ssbb/pipra/pcb/pipra.kicad_sch

## KiCad design pcb/pipra.kicad_sch (2025-05-22, an earlier design)

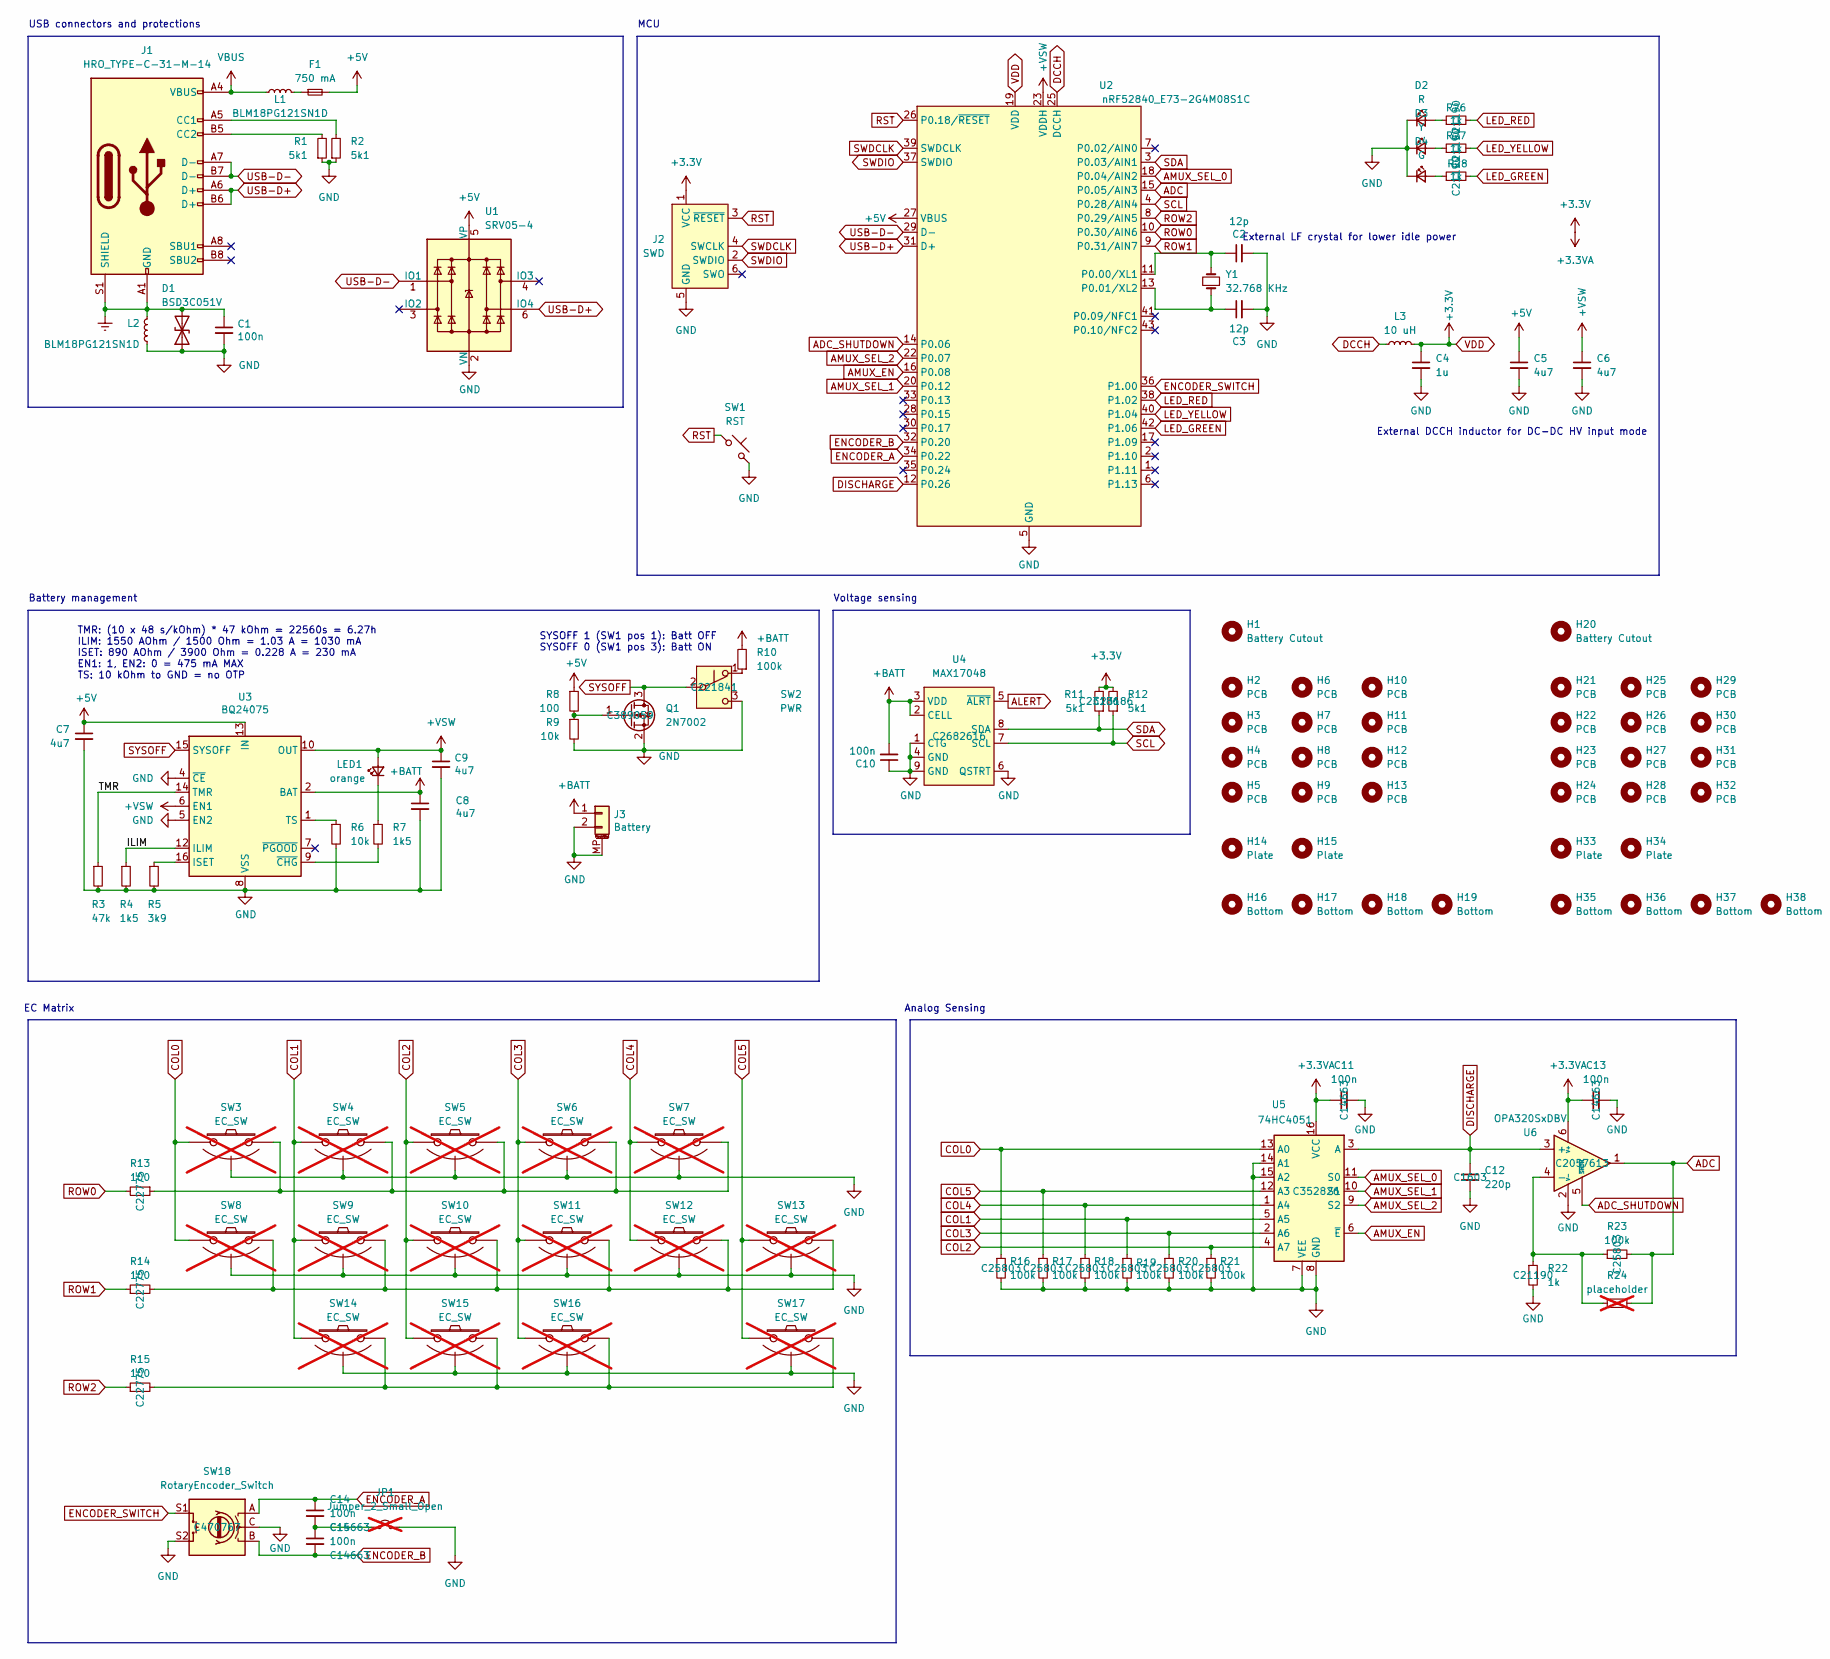
[picture p2: schematic pipra.kicad_sch, part in row 1, column 1]

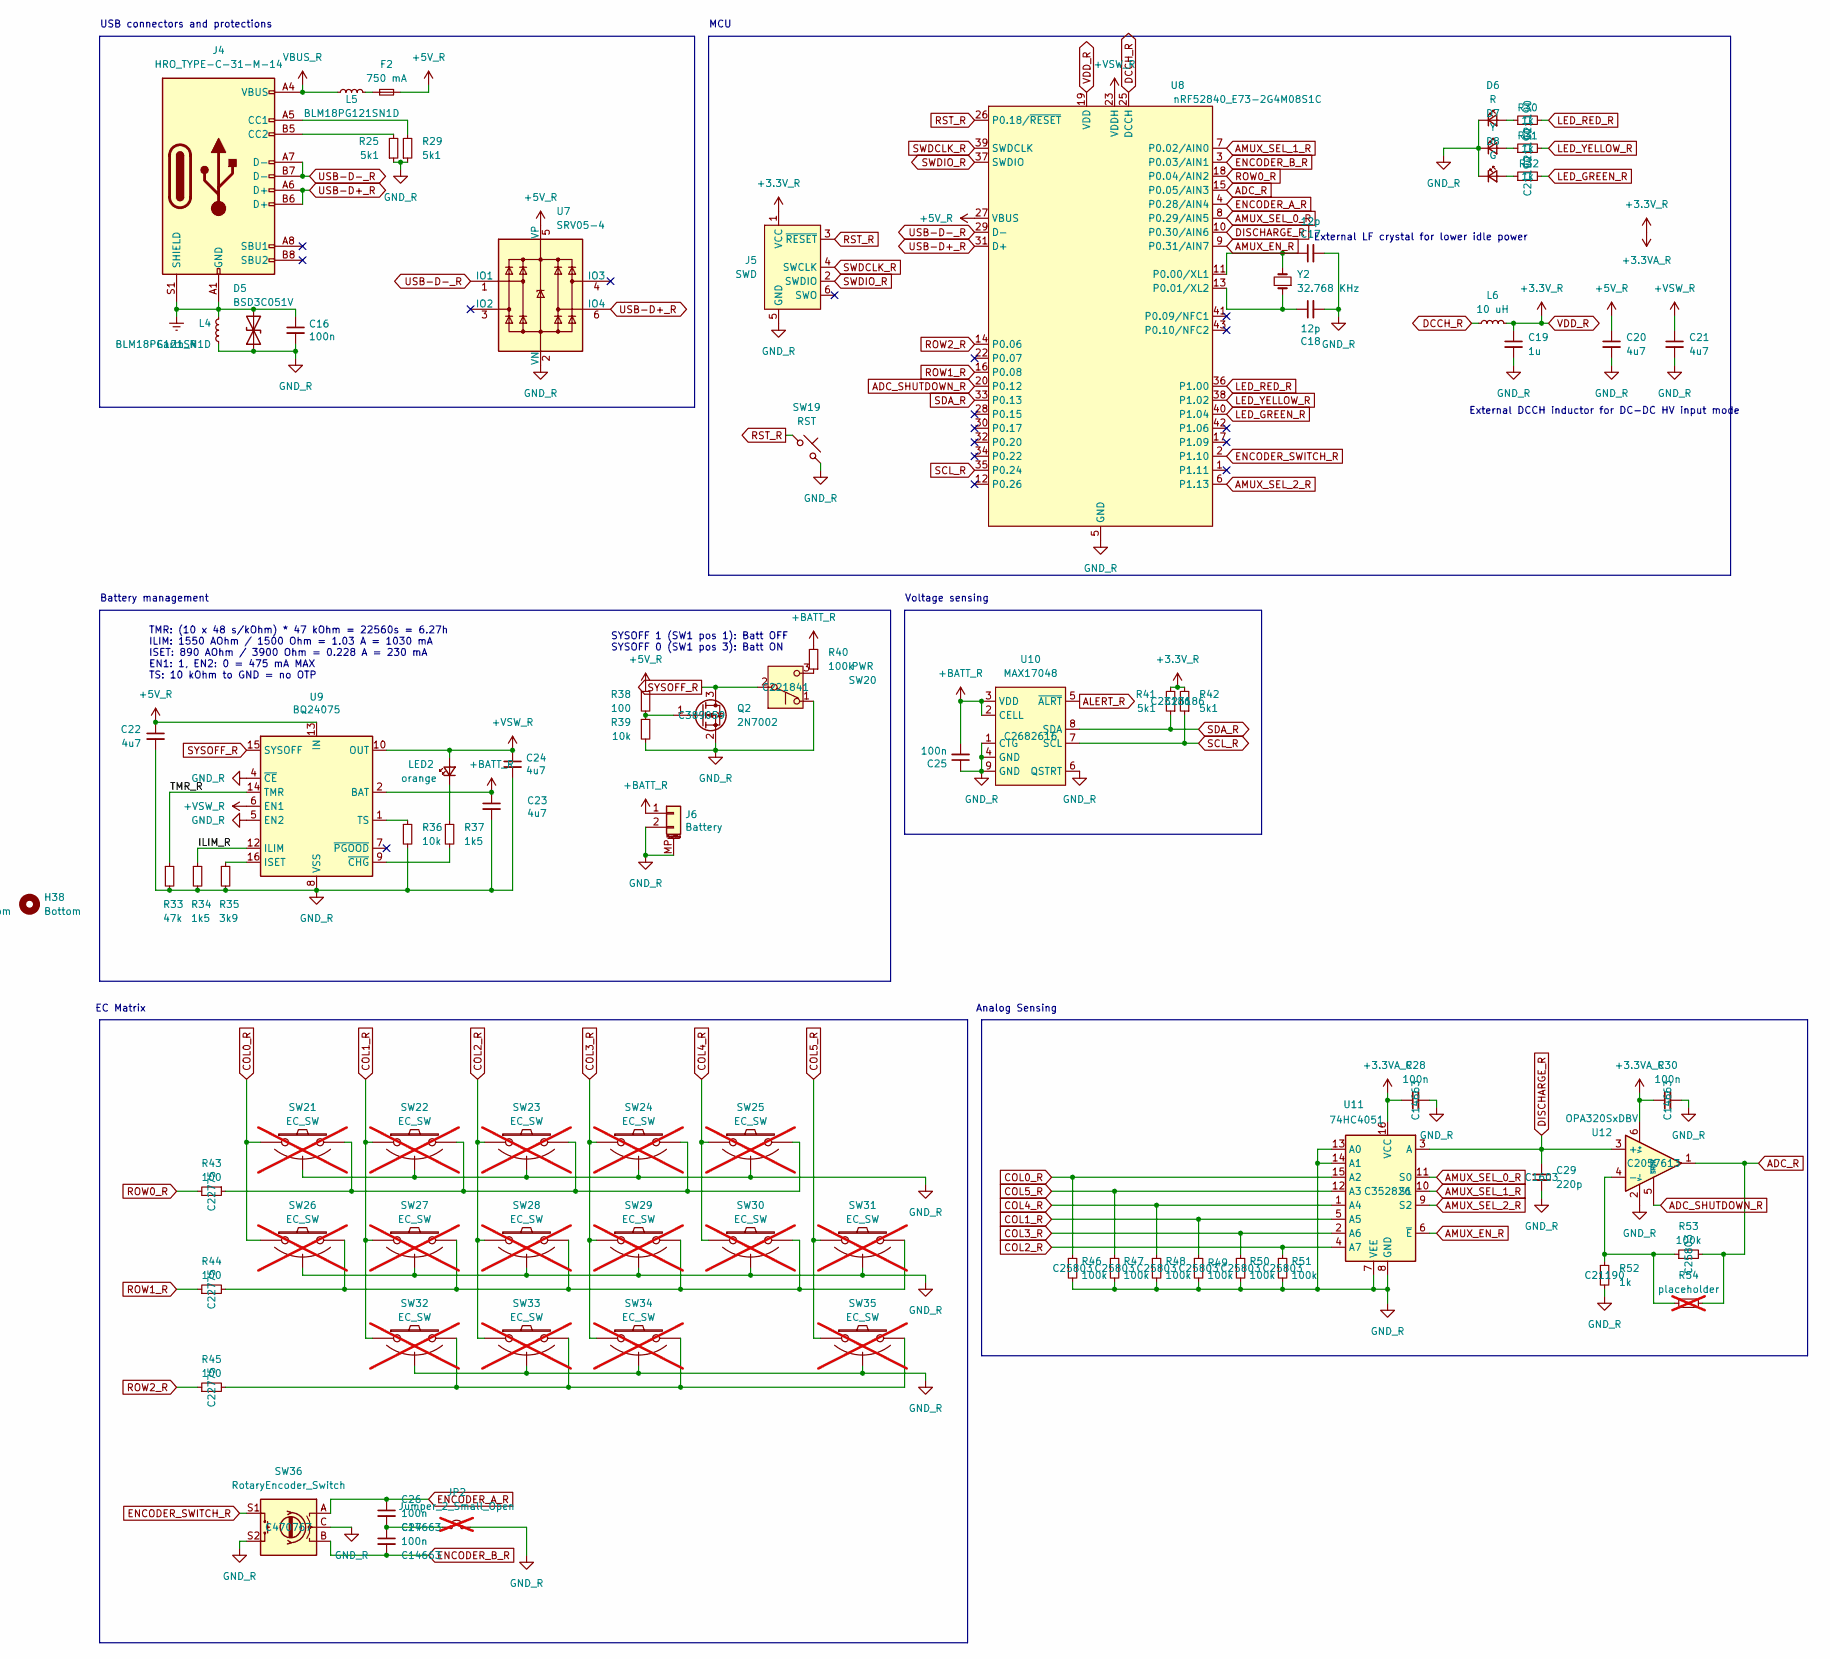
[picture p3: schematic pipra.kicad_sch, part in row 1, column 2]

Parts:
C1, C10, C11, C13, C14, C15, C16, C25, C26, C27, C28, C30: 100n; C_0603_1608Metric; LCSC C14663
C2, C3, C17, C18: 12p; C_0603_1608Metric; LCSC C38523
C4, C19: 1u; C_0603_1608Metric; LCSC C15849
C5, C6, C7, C8, C9, C20, C21, C22, C23, C24: 4u7; C_0603_1608Metric; LCSC C19666
C12, C29: 220p; C_0603_1608Metric; LCSC C1603
D1, D5: BSD3C051V; D_SOD-323; LCSC C151996
D2, D6: R; LED_D3.0mm; LCSC C2895165
D3, D7: Y; LED_D3.0mm; LCSC C2895167
D4, D8: G; LED_D3.0mm; LCSC C2895166
F1, F2: 750 mA; Fuse_0603_1608Metric; LCSC C914092
H1, H20: Battery Cutout; Battery_HAC-006
H2, H3, H4, H5, H6, H7, H8, H9, H10, H11, H12, H13, H21, H22, H23, H24, H25, H26, H27, H28, H29, H30, H31, H32: PCB; MountingHole_2.2mm_M2
H14, H15, H33, H34: Plate; MountingHole_4mm
H16, H17, H18, H19, H35, H36, H37, H38: Bottom; MountingHole_3.5mm
J1, J4: HRO_TYPE-C-31-M-14; USB_C_Receptacle_HRO_TYPE-C-31-M-12; LCSC C165948
J2, J5: SWD; CON_TC2030_outlined
J3, J6: Battery; Molex_Pico-EZmate_78171-0002_1x02-1MP_P1.20mm_Vertical; LCSC C505023
JP1, JP2: Jumper_2_Small_Open; SolderJumper-2_P1.3mm_Open_RoundedPad1.0x1.5mm; not fitted
L1, L2, L4, L5: BLM18PG121SN1D; L_0603_1608Metric; LCSC C14709
L3, L6: 10 uH; L_0603_1608Metric; LCSC C92982
LED1, LED2: orange; LED_0603_1608Metric; LCSC C401116
Q1, Q2: 2N7002; SOT-23; LCSC C389059
R1, R2, R11, R12, R25, R29, R41, R42: 5k1; R_0603_1608Metric; LCSC C23186
R3, R33: 47k; R_0603_1608Metric; LCSC C25819
R4, R7, R34, R37: 1k5; R_0603_1608Metric; LCSC C22843
R5, R35: 3k9; R_0603_1608Metric; LCSC C23018
R6, R9, R36, R39: 10k; R_0603_1608Metric; LCSC C25804
R8, R13, R14, R15, R38, R43, R44, R45: 100; R_0603_1608Metric; LCSC C22775
R10, R16, R17, R18, R19, R20, R21, R23, R40, R46, R47, R48, R49, R50, R51, R53: 100k; R_0603_1608Metric; LCSC C25803
R22, R26, R27, R28, R30, R31, R32, R52: 1k; R_0603_1608Metric; LCSC C21190
R24, R54: placeholder; R_0603_1608Metric; not fitted
SW1, SW19: RST; Panasonic_EVQPUL_EVQPUC; LCSC C79174
SW2, SW20: PWR; SW_SPDT_PCM12; LCSC C221841
SW3, SW4, SW5, SW6, SW7, SW8, SW9, SW10, SW11, SW12, SW13, SW14, SW15, SW16, SW17, SW21, SW22, SW23, SW24, SW25, SW26, SW27, SW28, SW29, SW30, SW31, SW32, SW33, SW34, SW35: EC_SW; EC_Pad_L84; not fitted
SW18, SW36: RotaryEncoder_Switch; RotaryEncoder_Alps_EC12E-Switch_Vertical_H20mm; LCSC C470767
U1, U7: SRV05-4; SOT-23-6; LCSC C2836319
U2, U8: nRF52840_E73-2G4M08S1C; LCSC C356849
U3, U9: BQ24075; VQFN-16-1EP_3x3mm_P0.5mm_EP1.6x1.6mm; LCSC C15464
U4, U10: MAX17048; TDFN-8-1EP_2x2mm_P0.5mm_EP0.8x1.2mm; LCSC C2682616
U5, U11: 74HC4051; TSSOP-16_4.4x5mm_P0.65mm; LCSC C352826
U6, U12: OPA320SxDBV; SOT-23-6; LCSC C2057613
Y1, Y2: 32.768 KHz; Crystal_SMD_2012-2Pin_2.0x1.2mm; LCSC C55208

Connections:
+3.3V: C4.1, C11.1, C13.1, J2.1 (VCC), L3.2, R11.2, R12.2, U2.19 (VDD), U5.16 (VCC), U6.6 (V+)
+3.3V_R: C19.1, C28.1, C30.1, J5.1 (VCC), L6.2, R41.2, R42.2, U8.19 (VDD), U11.16 (VCC), U12.6 (V+)
+5V: C5.1, C7.1, F1.2, R8.1, U1.5 (VP), U2.27 (VBUS), U3.13 (IN)
+5V_R: C20.1, C22.1, F2.2, R38.1, U7.5 (VP), U8.27 (VBUS), U9.13 (IN)
+BATT: C8.1, C10.2, J3.1, R10.2, U3.2 (BAT), U3.3 (BAT), U4.2 (CELL), U4.3 (VDD)
+BATT_R: C23.1, C25.2, J6.1, R40.2, U9.2 (BAT), U9.3 (BAT), U10.2 (CELL), U10.3 (VDD)
+VSW: C6.1, C9.1, LED1.2 (A), U2.23 (VDDH), U3.6 (EN1), U3.10 (OUT), U3.11 (OUT)
+VSW_R: C21.1, C24.1, LED2.2 (A), U8.23 (VDDH), U9.6 (EN1), U9.10 (OUT), U9.11 (OUT)
ADC: R23.2, R24.1, U2.15 (P0.05/AIN3), U6.1
ADC_R: R53.2, R54.1, U8.15 (P0.05/AIN3), U12.1
ADC_SHUTDOWN: U2.14 (P0.06), U6.5 (~SHDN)
ADC_SHUTDOWN_R: U8.20 (P0.12), U12.5 (~SHDN)
ALERT: U4.5 (~ALRT)
ALERT_R: U10.5 (~ALRT)
AMUX_EN: U2.16 (P0.08), U5.6 (~E)
AMUX_EN_R: U8.9 (P0.31/AIN7), U11.6 (~E)
AMUX_SEL_0: U2.18 (P0.04/AIN2), U5.11 (S0)
AMUX_SEL_0_R: U8.8 (P0.29/AIN5), U11.11 (S0)
AMUX_SEL_1: U2.20 (P0.12), U5.10 (S1)
AMUX_SEL_1_R: U8.7 (P0.02/AIN0), U11.10 (S1)
AMUX_SEL_2: U2.22 (P0.07), U5.9 (S2)
AMUX_SEL_2_R: U8.6 (P1.13), U11.9 (S2)
COL0: R16.1, SW3.1, SW8.1, U5.13 (A0)
COL0_R: R46.1, SW21.1, SW26.1, U11.15 (A2)
COL1: R19.1, SW4.1, SW9.1, SW14.1, U5.5 (A5)
COL1_R: R49.1, SW22.1, SW27.1, SW32.1, U11.5 (A5)
COL2: R21.1, SW5.1, SW10.1, SW15.1, U5.4 (A7)
COL2_R: R51.1, SW23.1, SW28.1, SW33.1, U11.4 (A7)
COL3: R20.1, SW6.1, SW11.1, SW16.1, U5.2 (A6)
COL3_R: R50.1, SW24.1, SW29.1, SW34.1, U11.2 (A6)
COL4: R18.1, SW7.1, SW12.1, U5.1 (A4)
COL4_R: R48.1, SW25.1, SW30.1, U11.1 (A4)
COL5: R17.1, SW13.1, SW17.1, U5.12 (A3)
COL5_R: R47.1, SW31.1, SW35.1, U11.12 (A3)
DCCH: L3.1, U2.25 (DCCH)
DCCH_R: L6.1, U8.25 (DCCH)
DISCHARGE: C12.1, U2.12 (P0.26), U5.3 (A), U6.3 (+)
DISCHARGE_R: C29.1, U8.10 (P0.30/AIN6), U11.3 (A), U12.3 (+)
ENCODER_A: C14.1, SW18.A, U2.34 (P0.22)
ENCODER_A_R: C26.1, SW36.A, U8.4 (P0.28/AIN4)
ENCODER_B: C15.2, SW18.B, U2.32 (P0.20)
ENCODER_B_R: C27.2, SW36.B, U8.3 (P0.03/AIN1)
ENCODER_SWITCH: SW18.S1, U2.36 (P1.00)
ENCODER_SWITCH_R: SW36.S1, U8.2 (P1.10)
Earth: C1.1, D1.2 (A2), J1.A1 (GND), J1.A12 (GND), J1.B1 (GND), J1.B12 (GND), J1.S1 (SHIELD), L2.1
Earth_R: C16.1, D5.2 (A2), J4.A1 (GND), J4.A12 (GND), J4.B1 (GND), J4.B12 (GND), J4.S1 (SHIELD), L4.1
GND: C1.2, C2.2, C3.2, C4.2, C5.2, C6.2, C7.2, C8.2, C9.2, C10.1, C11.2, C12.2, C13.2, D1.1 (A1), D2.1 (K), D3.1 (K), D4.1 (K), J2.5 (GND), J3.2, J3.MP (MountPin), JP1.2 (B), L2.2, Q1.2 (S), R1.1, R2.1, R3.2, R4.2, R5.2, R6.2, R9.2, R16.2, R17.2, R18.2, R19.2, R20.2, R21.2, R22.2, SW1.2, SW2.3 (C), SW3.3 (SG), SW4.3 (SG), SW5.3 (SG), SW6.3 (SG), SW7.3 (SG), SW8.3 (SG), SW9.3 (SG), SW10.3 (SG), SW11.3 (SG), SW12.3 (SG), SW13.3 (SG), SW14.3 (SG), SW15.3 (SG), SW16.3 (SG), SW17.3 (SG), SW18.C, SW18.S2, U1.2 (VN), U2.5 (GND), U2.21 (GND), U2.24 (GND), U3.4 (~CE), U3.5 (EN2), U3.8 (VSS), U3.17 (VSS), U4.1 (CTG), U4.4 (GND), U4.6 (QSTRT), U4.9 (GND), U5.7 (VEE), U5.8 (GND), U5.14 (A1), U5.15 (A2), U6.2 (V-)
GND_R: C16.2, C17.2, C18.2, C19.2, C20.2, C21.2, C22.2, C23.2, C24.2, C25.1, C28.2, C29.2, C30.2, D5.1 (A1), D6.1 (K), D7.1 (K), D8.1 (K), J5.5 (GND), J6.2, J6.MP (MountPin), JP2.2 (B), L4.2, Q2.2 (S), R25.1, R29.1, R33.2, R34.2, R35.2, R36.2, R39.2, R46.2, R47.2, R48.2, R49.2, R50.2, R51.2, R52.2, SW19.2, SW20.1 (A), SW21.3 (SG), SW22.3 (SG), SW23.3 (SG), SW24.3 (SG), SW25.3 (SG), SW26.3 (SG), SW27.3 (SG), SW28.3 (SG), SW29.3 (SG), SW30.3 (SG), SW31.3 (SG), SW32.3 (SG), SW33.3 (SG), SW34.3 (SG), SW35.3 (SG), SW36.C, SW36.S2, U7.2 (VN), U8.5 (GND), U8.21 (GND), U8.24 (GND), U9.4 (~CE), U9.5 (EN2), U9.8 (VSS), U9.17 (VSS), U10.1 (CTG), U10.4 (GND), U10.6 (QSTRT), U10.9 (GND), U11.7 (VEE), U11.8 (GND), U11.13 (A0), U11.14 (A1), U12.2 (V-)
ILIM: R4.1, U3.12 (ILIM)
ILIM_R: R34.1, U9.12 (ILIM)
LED_GREEN: R28.2, U2.42 (P1.06)
LED_GREEN_R: R32.2, U8.40 (P1.04)
LED_RED: R26.2, U2.38 (P1.02)
LED_RED_R: R30.2, U8.36 (P1.00)
LED_YELLOW: R27.2, U2.40 (P1.04)
LED_YELLOW_R: R31.2, U8.38 (P1.02)
unnamed: C2.1, U2.11 (P0.00/XL1), Y1.2
unnamed: C3.1, U2.13 (P0.01/XL2), Y1.1
unnamed: C14.2, C15.1, JP1.1 (A)
unnamed: C17.1, U8.11 (P0.00/XL1), Y2.2
unnamed: C18.1, U8.13 (P0.01/XL2), Y2.1
unnamed: C26.2, C27.1, JP2.1 (A)
unnamed: D2.2 (A), R26.1
unnamed: D3.2 (A), R27.1
unnamed: D4.2 (A), R28.1
unnamed: D6.2 (A), R30.1
unnamed: D7.2 (A), R31.1
unnamed: D8.2 (A), R32.1
unnamed: F1.1, L1.2
unnamed: F2.1, L5.2
unnamed: J1.A5 (CC1), R2.2
unnamed: J1.B5 (CC2), R1.2
unnamed: J4.A5 (CC1), R29.2
unnamed: J4.B5 (CC2), R25.2
unnamed: LED1.1 (K), R7.1
unnamed: LED2.1 (K), R37.1
unnamed: Q1.1 (G), R8.2, R9.1
unnamed: Q2.1 (G), R38.2, R39.1
unnamed: R5.1, U3.16 (ISET)
unnamed: R6.1, U3.1 (TS)
unnamed: R7.2, U3.9 (~CHG)
unnamed: R10.1, SW2.1 (A)
unnamed: R13.1, SW3.2, SW4.2, SW5.2, SW6.2, SW7.2
unnamed: R14.2, SW8.2, SW9.2, SW10.2, SW11.2, SW12.2, SW13.2
unnamed: R15.2, SW14.2, SW15.2, SW16.2, SW17.2
unnamed: R22.1, R23.1, R24.2, U6.4 (-)
unnamed: R35.1, U9.16 (ISET)
unnamed: R36.1, U9.1 (TS)
unnamed: R37.2, U9.9 (~CHG)
unnamed: R40.1, SW20.3 (C)
unnamed: R43.1, SW21.2, SW22.2, SW23.2, SW24.2, SW25.2
unnamed: R44.2, SW26.2, SW27.2, SW28.2, SW29.2, SW30.2, SW31.2
unnamed: R45.2, SW32.2, SW33.2, SW34.2, SW35.2
unnamed: R52.1, R53.1, R54.2, U12.4 (-)
ROW0: R13.2, U2.10 (P0.30/AIN6)
ROW0_R: R43.2, U8.18 (P0.04/AIN2)
ROW1: R14.1, U2.9 (P0.31/AIN7)
ROW1_R: R44.1, U8.16 (P0.08)
ROW2: R15.1, U2.8 (P0.29/AIN5)
ROW2_R: R45.1, U8.14 (P0.06)
RST: J2.3 (~RESET), SW1.1, U2.26 (P0.18/~RESET)
RST_R: J5.3 (~RESET), SW19.1, U8.26 (P0.18/~RESET)
SCL: R12.1, U2.4 (P0.28/AIN4), U4.7 (SCL)
SCL_R: R42.1, U8.35 (P0.24), U10.7 (SCL)
SDA: R11.1, U2.3 (P0.03/AIN1), U4.8 (SDA)
SDA_R: R41.1, U8.33 (P0.13), U10.8 (SDA)
SWDCLK: J2.4 (SWCLK), U2.39 (SWDCLK)
SWDCLK_R: J5.4 (SWCLK), U8.39 (SWDCLK)
SWDIO: J2.2 (SWDIO), U2.37 (SWDIO)
SWDIO_R: J5.2 (SWDIO), U8.37 (SWDIO)
SYSOFF: Q1.3 (D), SW2.2 (B), U3.15 (SYSOFF)
SYSOFF_R: Q2.3 (D), SW20.2 (B), U9.15 (SYSOFF)
TMR: R3.1, U3.14 (TMR)
TMR_R: R33.1, U9.14 (TMR)
USB-D+: J1.A6 (D+), J1.B6 (D+), U1.6 (IO4), U2.31 (D+)
USB-D+_R: J4.A6 (D+), J4.B6 (D+), U7.6 (IO4), U8.31 (D+)
USB-D-: J1.A7 (D-), J1.B7 (D-), U1.1 (IO1), U2.29 (D-)
USB-D-_R: J4.A7 (D-), J4.B7 (D-), U7.1 (IO1), U8.29 (D-)
VBUS: J1.A4 (VBUS), J1.A9 (VBUS), J1.B4 (VBUS), J1.B9 (VBUS), L1.1
VBUS_R: J4.A4 (VBUS), J4.A9 (VBUS), J4.B4 (VBUS), J4.B9 (VBUS), L5.1

Notes on the sheet:
Analog Sensing
USB connectors and protections
EC Matrix
Battery management
TMR: (10 x 48 s/kOhm) * 47 kOhm = 22560s = 6.27h ILIM: 1550 AOhm / 1500 Ohm = 1.03 A = 1030 mA ISET: 890 AOhm / 3900 Ohm = 0.228 A = 230 mA EN1: 1, EN2: 0 = 475 mA MAX TS: 10 kOhm to GND = no OTP
MCU
External DCCH inductor for DC-DC HV input mode
SYSOFF 1 (SW1 pos 1): Batt OFF SYSOFF 0 (SW1 pos 3): Batt ON
External LF crystal for lower idle power
Voltage sensing
